jcmkk3/trochilidae/rufous/rufous_choc_pcb_back.png

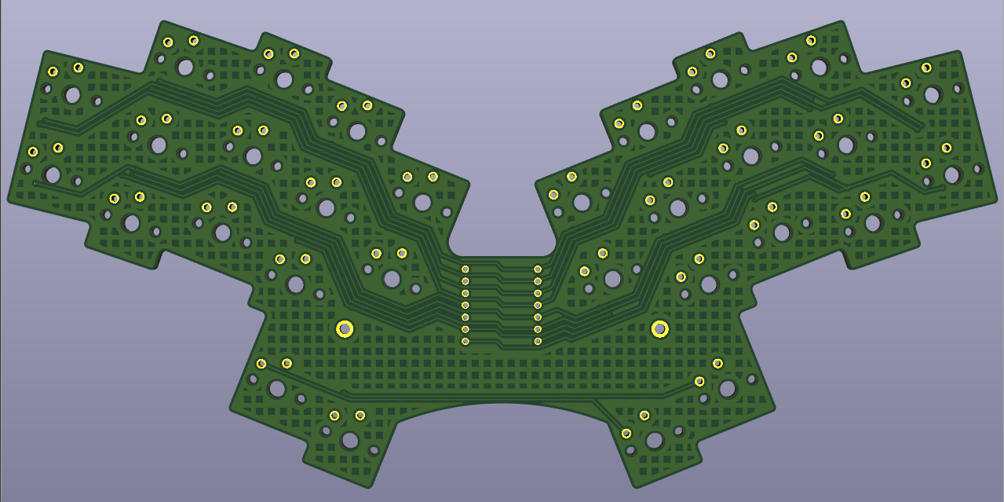
rufous/rufous_choc_pcb_back.png
