jcmkk3/trochilidae/rufous/rufous_choc_pcb_front.png

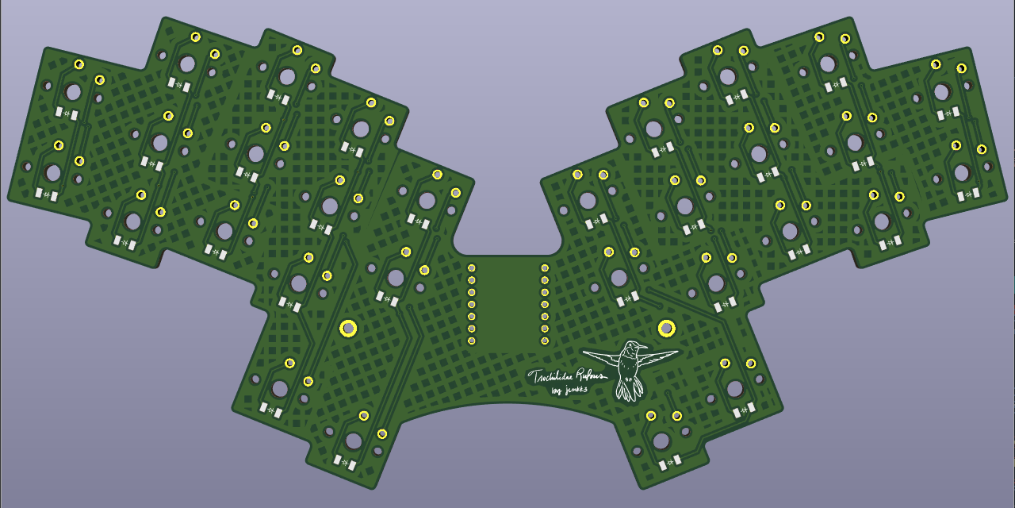
rufous/rufous_choc_pcb_front.png
