jcmkk3/trochilidae/workshop/three-piece.yml

units:
  # Parameters
  # ==========
  cx: 18.5        # Key spacing horizontal
  cy: 17.5        # Key spacing vertical
  sf: 16          # Switch footprint (square)
  angle: 22       # Angle between halves
  pinky_splay: 0  # Degrees of splay between pinky and ring columns
  ring_splay: 0   # Degrees of splay between ring and index columns
  
  # *Note:* not all supported changes are parameterized

points:
  rotate: -angle + pinky_splay + ring_splay
  mirror:
    ref: matrix_inner_top
    shift: [0.5sf, 0.5sf]
    distance: 13

  # Zones
  # =====
  # There are two zones defined: `matrix` and `thumb`
  # - The `matrix` covers all keys used by the pinky - index fingers
  # - The `thumb` zone sits below the matrix keys
  #
  # Top level attributes of `spread`, `stagger`, and `rotate` are defined at the column level
  # - `spread` determines the distance between columns and uses the parameter `cx`
  # - `stagger` is the vertical differences between columns
  #   It is typically based on a fraction of the vertical key spacing `cy`
  # - `rotate` is the "splay" of the column
  #   This should be controlled with the appropriate parameters and not overriden directly
  #
  # Row level attributes serve various utility purposes
  # - `row.skip` is used to remove the bottom key in the pinky and inner columns
  # - `bind` is used to apply extra padding to specific keys in order to fill gaps
  #   or shape the outline produced by `type: keys` in the outline section
  # - `row_net` and `column_net` are used to define the connections between the keys
  #   and other components as defined in the `key.footprints` or `pcb` sections of the config
  # - `tags` are helpers that allow later sections like `outlines` filter selections
  #   to those specific keys
  zones.matrix:
    rows:
      bottom.padding: cy
      home.padding: cy
      top.padding: cy
    columns.pinky:
      spread: cx
      rows:
        bottom.skip: true
        top:
          bind: [0,0.5cx,0.5cy,0]
          row_net: P0
          column_net: P6
          tags:
            matrix: true
        home:
          bind: [0.5cy,0.5cx,0,0]
          row_net: P2
          column_net: P6
          tags:
            matrix: true
        top.mirror:
          row_net: P1
          column_net: P10
        home.mirror:
          row_net: P3
          column_net: P10
    columns.ring:
      spread: cx
      stagger: 0.5cy
      rotate: -pinky_splay
      rows:
        top:
          bind: [0,0.5cx,0.5cy,0]
          row_net: P1
          column_net: P6
          tags:
            matrix: true
        home:
          bind: [0,0.5cx,0,0]
          row_net: P3
          column_net: P6
          tags:
            matrix: true
        bottom:
          bind: [0.5cy,0,0,0]
          row_net: P4
          column_net: P6
          tags:
            matrix: true
        top.mirror:
          row_net: P0
          column_net: P10
        home.mirror:
          row_net: P2
          column_net: P10
        bottom.mirror:
          row_net: P5
          column_net: P9
    columns.middle:
      spread: cx
      stagger: 0.25cy
      rotate: -ring_splay
      rows:
        top:
          bind: [0,0,0.5cy,0]
          row_net: P0
          column_net: P7
          tags:
            matrix: true
        home:
          bind: [0,0.5cx,0,0]
          row_net: P2
          column_net: P7
          tags:
            matrix: true
        bottom:
          bind: [0.5cy,0.5cx,0,0.5cx]
          row_net: P5
          column_net: P6
          tags:
            matrix: true
        top.mirror:
          row_net: P1
          column_net: P9
        home.mirror:
          row_net: P3
          column_net: P9
        bottom.mirror:
          row_net: P4
          column_net: P9
    columns.index:
      spread: cx
      stagger: -0.25cy
      rows:
        top:
          bind: [0,0,0.5cy,0.5cx]
          row_net: P1
          column_net: P7
          tags:
            matrix: true
        home:
          row_net: P3
          column_net: P7
          tags:
            matrix: true
        bottom:
          bind: [0.5cy,0,0,0]
          row_net: P4
          column_net: P7
          tags:
            matrix: true
        top.mirror:
          row_net: P0
          column_net: P9
        home.mirror:
          row_net: P2
          column_net: P9
        bottom.mirror:
          row_net: P5
          column_net: P8
    columns.inner:
      spread: cx
      stagger: -0.5cy
      rows:
        bottom.skip: true
        top:
          bind: [0,0,0.5cy,0.5cx]
          row_net: P0
          column_net: P8
          tags:
            matrix: true
        home:
          bind: [0.5cy,0,0,0.5cx]
          row_net: P2
          column_net: P8
          tags:
            matrix: true
        top.mirror:
          row_net: P1
          column_net: P8
        home.mirror:
          row_net: P3
          column_net: P8
  zones.thumb:
    anchor:
      ref: matrix_index_bottom
      shift: [0.25cx, -22]
    rows.thumb:
    columns.outer:
      rows:
        thumb:
          bind: [2cy, 0.5cx, 0, 0]
          row_net: P5
          column_net: P7
          tags:
            center_bottom: true
        thumb.mirror:
          row_net: P4
          column_net: P10
    columns.inner:
      spread: cx
      stagger: -0.25cy
      rows:
        thumb:
          bind: [2cy, 0, 0, 0]
          row_net: P4
          column_net: P8
          tags:
            center_bottom: true
        thumb.mirror:
          row_net: P5
          column_net: P10
outlines:
  exports:
    # The below outlines are intentionally split out in order
    # to view the intermediate steps during transformation
    _outer_raw:
      - type: keys
        side: left
        size: sf
        tags: [center_bottom]
      - type: keys
        side: right
        size: sf
        tags: [center_bottom]
    _center_raw:
      - type: polygon
        points:
        - ref: matrix_inner_top
          shift: [0,-0.7cy]
        - ref: mirror_matrix_inner_top
          shift: [0,-0.7cy]
        - ref: mirror_thumb_inner_thumb
        - ref: thumb_inner_thumb
    _center:
      - name: _center_raw
        fillet: 3  # The inner rounding where the glue meets the top center keys
      - operation: subtract
        type: circle
        anchor:
          ref: [thumb_inner_thumb, mirror_thumb_inner_thumb]
          shift: [0, 0.5sf - 60]
        radius: 60  # Should be the same as the last number in `shift` above
    _combined:
      - _outer_raw
      - _center
      - operation: subtract
        type: polygon
        points:
        - ref: matrix_inner_home
          shift: [-2cx,-0.55cy]
        - ref: mirror_matrix_inner_home
          shift: [-2cx,-0.55cy]
        - ref: mirror_matrix_index_top
        - ref: matrix_index_top
    _switch_cutouts:
      - type: keys
        side: left
        size: 14
        bound: false
        tags: [center_bottom]
      - type: keys
        side: right
        size: 14
        bound: false
        tags: [center_bottom]
    panel:
      - name: _combined
        fillet: 1
    center_switch_plate:
      - name: _combined
        fillet: 1
      - operation: stack
        name: _switch_cutouts
        fillet: 0.5
    one_side_switch_plate:
      - type: keys
        side: left
        size: sf
        tags: [matrix]
      - operation: subtract
        type: keys
        side: left
        size: 14
        tags: [matrix]
        bound: false
points.key:
  footprints:
    - type: choc
      nets:
        from: =row_net
        to: =colrow
      params:
        keycaps: true
    - type: diode
      anchor:
        shift: [0, -4.7]
        rotate: 180
      nets:
        from: =colrow
        to: =column_net
      params:
        through_hole: false
pcbs:
  rufous:
    outlines:
      main:
        outline: panel
    footprints:
      - type: xiao
        anchor:
          ref: [matrix_inner_top, mirror_matrix_inner_top]
          shift: [-xiao_x / 2, -xiao_y - 0.7cy]
          # Final vertical shift should be the same as the vertical shift from
          # `_center_raw` polygon defined in the outline section above
