jcmkk3/trochilidae/workshop/vault35.yml

units:
  visual_x: 1
  visual_y: 1
points:
  zones.alpha:
    key:
      width: U
      height: U
    rows:
      r4:
        padding: U
        shift: [0.75U, 0]
      r3:
        padding: U
        shift: [0.25U, 0]
      r2:
        padding: U
    columns:
      one:
        rows:
          r4:
            width: 1.75U
            shift: [0.75U / 2, 0]
          r3:
            width: 1.25U
            shift: [0.25U / 2, 0]
      two:
      three:
      four:
      five:
      six:
      seven:
      eight:
      nine:
      ten:
        rows:
          r4:
            width: 1.25U
            shift: [1.75U / 2, 0]
          r3:
            width: 1.75U
            shift: [1.25U / 2, 0]
      eleven:
        rows:
          r4.skip: true
          r3.skip: true
  zones.r5:
    anchor:
      ref: alpha_one_r4
      shift: [1.25U, -U]
    key:
      width: U
      height: U
    rows.row:
    columns:
      one:
        key.width: 1.25U
      two:
        key.width: 1.25U
        spread: 1.25U
      three:
        key.width: 3U
        spread: 2U + (0.25U / 2)
      four:
        key.width: 1.25U
        spread: 2U + (0.25U / 2)
      five:
        key.width: 1.25U
        spread: 1.25U
